MatthiasWM/newt_dongle/3d-parts/jigs/Detailer2.002.stl

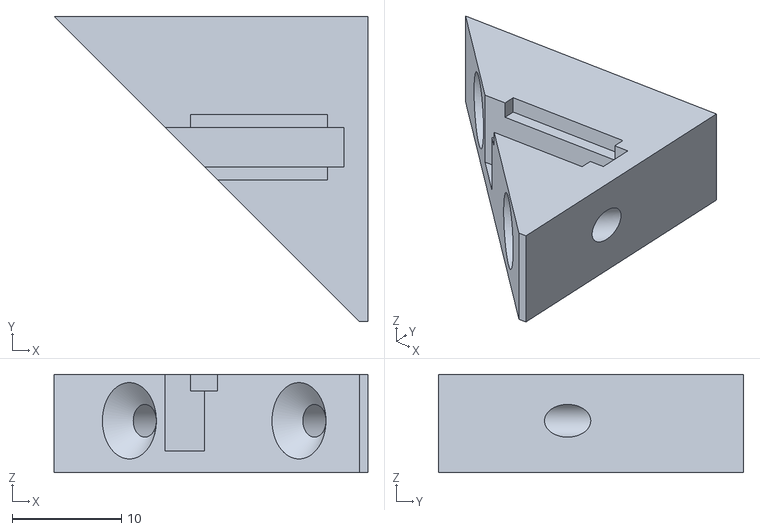
[picture p41: CAD file, 2025-05-21]
3d-parts/jigs/Detailer2.002.stl
28.8 x 28.0 x 9.00
