MatthiasWM/newt_dongle/3d-parts/DongleCase2.012-Bottom.stl

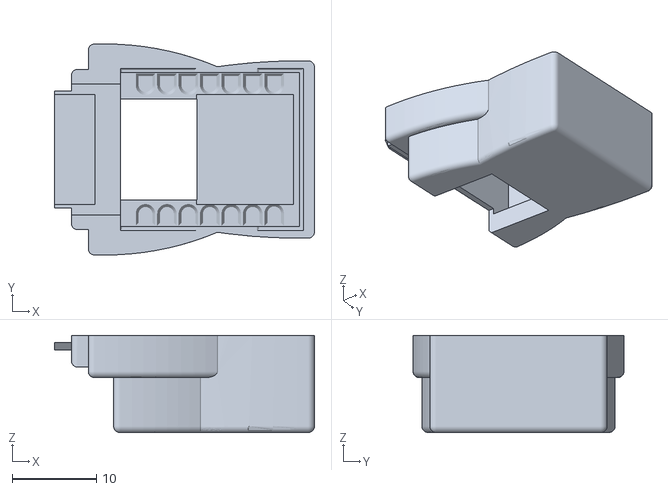
[picture p42: CAD file, 2025-05-21]
3d-parts/DongleCase2.012-Bottom.stl
30.8 x 25.0 x 11.5
