MatthiasWM/newt_dongle/3d-parts/jigs/Bender.003-Bender.stl

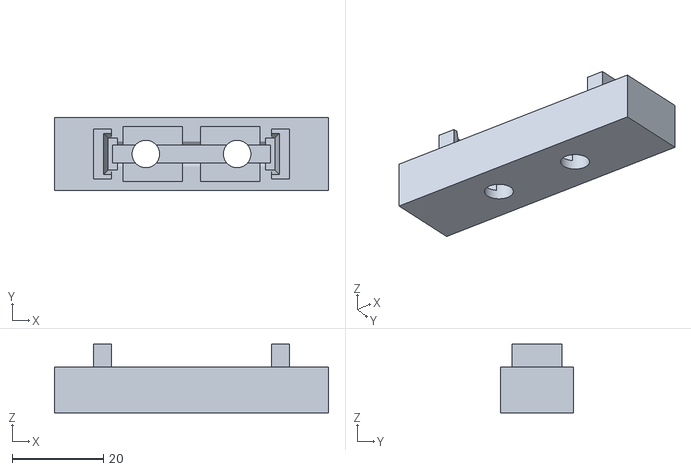
[picture p43: CAD file, 2025-05-10]
3d-parts/jigs/Bender.003-Bender.stl
60.0 x 16.0 x 15.0
