MatthiasWM/newt_dongle/3d-parts/DongleCase2.012-Top.stl

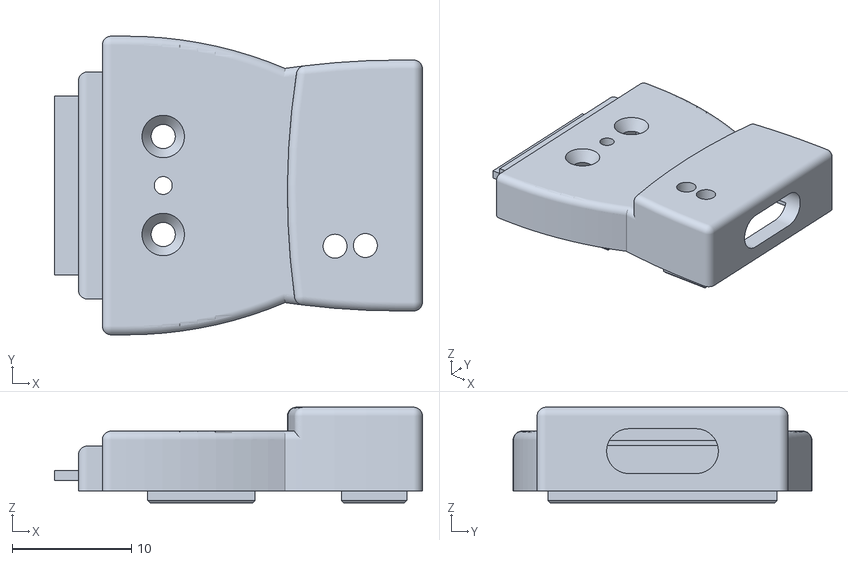
[picture p44: CAD file, 2025-05-21]
3d-parts/DongleCase2.012-Top.stl
30.8 x 25.0 x 8.00
