MatthiasWM/newt_dongle/Firmware/common/Filters/DTRSwitch.h

//
// SPDX-License-Identifier: MIT
// Copyright (c) 2025 Matthias Melcher, robowerk.de
//

#ifndef ND_FILTERS_DTR_SWITCH_H
#define ND_FILTERS_DTR_SWITCH_H

#include "common/Pipe.h"

namespace nd {

class DTRSwitch: public Pipe {
    typedef Pipe super;
    friend class ToDockPipe;
    friend class ToCDCPipe;

    class ToDockPipe *dock_ = nullptr; // Pipe to the Dock emulator
    class ToCDCPipe *cdc_ = nullptr;   // Pipe to the USB CDC port
public:
    bool dtr_set = false; // If true, route to CDC, else route to Dock.

    DTRSwitch();
    ~DTRSwitch() override;

    /// Publicly accessible pipe to the Dock emulator.
    Pipe &dock;
    /// Publicly accessible pipe to the USB CDC port.
    Pipe &cdc;

    // -- Pipe Stuff
    Result send(Event event) override;
    Result rush(Event event) override;
    Result rush_back(Event event) override;

};

} // namespace nd

#endif // ND_FILTERS_DTR_SWITCH_H
