MatthiasWM/newt_dongle/Firmware/Systems/RP2040/PicoAsyncLog.h

//
// SPDX-License-Identifier: MIT
// Copyright (c) 2025 Matthias Melcher, robowerk.de
//

#ifndef ND_PICO_ASYNC_LOG_H
#define ND_PICO_ASYNC_LOG_H

#include "common/Event.h"
#include "common/Logger.h"

#include <pico/util/queue.h>
#include <pico/time.h>

namespace nd {

class PicoAsyncLog : public Logger {
    static PicoAsyncLog *the_instance_;
    static void run_() { the_instance_->run(); }
    static queue_t queue_;
    absolute_time_t prev_event_time_ = nil_time;
    int dest_ = 0; // 0 = stdio, 1 = sd card
    void run();
public:
    PicoAsyncLog(int dest);
    ~PicoAsyncLog() override = default;
    void log(Event event, int pipe=0) override;
    void log(Result result, int pipe=0) override;
    void log(const char *message, int pipe=0) override;
    void logf(const char *message, ...) override;
};

} // namespace nd

#endif // ND_PICO_ASYNC_LOG_H
