MatthiasWM/newt_dongle/Firmware/Systems/RP2040/PicoCDCEndpoint.h

//
// SPDX-License-Identifier: MIT
// Copyright (c) 2025 Matthias Melcher, robowerk.de
//

#ifndef ND_PICO_CDC_ENDPOINT_H
#define ND_PICO_CDC_ENDPOINT_H  

#include "common/Endpoints/UARTEndpoint.h"

#include <cstdint>

namespace nd {

class PicoCDCEndpoint : public UARTEndpoint {
    static PicoCDCEndpoint *list_[4];
    uint32_t index_ = 0;
    uint32_t tx_num_pending_ = 0;   // Used to ensure a buffer flush at least ever 1 ms.
    uint32_t tx_timeout_ = 0;       // Used to ensure a buffer flush at least ever 1 ms.

public:
    static PicoCDCEndpoint *instance(uint32_t index);
    PicoCDCEndpoint(Scheduler &scheduler, uint32_t index);
    ~PicoCDCEndpoint();
    Result init() override;
    Result task() override;
    Result send(Event event) override;

    void set_bitrate(uint32_t new_bitrate) override;

    void device_changed_bitrate(uint32_t bitrate);
};

} // namespace nd

#endif // ND_PICO_CDC_ENDPOINT_H
